JuergenMH/diver_led_tools/DiverFlasher/simulation/LEDS_in_Reihe/Boost_Converter.asc

C1: polcap; 100µ; V=25 Irms=750m Rser=0.16 Lser=0
C2: polcap; 47µ; V=25 Irms=750m Rser=0.16 Lser=0
C3: polcap; 100µ; V=25 Irms=750m Rser=0.16 Lser=0
C4: cap; 100n
D1: LED; LXK2-PW14
D2: LED; LXK2-PW14
D3: schottky; RB058LAM100
L1: ind; 33µ; Ipk=2.8 Rser=0.2 Rpar=86577.4 Cpar=0
L2: ind; 33µ; Ipk=2.8 Rser=0.2 Rpar=86577.4 Cpar=0
M1: nmos; NTB52N10
R1: res; 1
R2: res; 1K
V1: voltage; 3.6; Rser=0.1
V2: voltage; PULSE(0 5 0 0.1µ 0.1µ 27µ 40µ 500)
Named nets: 0, SW_IN, SW_OUT, U_BAT, U_OUT
.tran 0 1.6ms 0 0.1µs startup
IL1 / D3
Anlauf = 7,2mA (<1ms)
Min    = 0,8A
Max    = 3,3A
Mittel = 2A
25KHz
Zum Regler-Eingang
(AD-PIC)
Pulsweite gesteuert duch PIC-Controller
