JuergenMH/diver_led_tools/DiverFlasher/simulation/LEDS_Parallel/Boost_Converter.asc

C1: polcap; 100µ; V=25 Irms=750m Rser=0.16 Lser=0
C2: polcap; 47µ; V=25 Irms=750m Rser=0.16 Lser=0
C3: polcap; 470µ; V=25 Irms=750m Rser=0.16 Lser=0
D1: LED; LXK2-PW14
D2: LED; LXK2-PW14
D3: schottky; RB058LAM100
L1: ind; 330µ; Ipk=2.8 Rser=0.23 Rpar=86577.4 Cpar=0
L3: ind; 100µ; Ipk=4 Rser=0.2 Rpar=10000 Cpar=0
M1: nmos; NTB52N10
R1: res; 1; tol=2 pwr=1
R2: res; 1; tol=2 pwr=1
V1: voltage; 3.7; Rser=0.1
V2: voltage; PULSE(0 5 0 1µ 1µ 25µ 50µ 100)
Named nets: 0, SW_IN, SW_OUT, U_BAT, U_OUT
.tran 0 5ms 0 0.002ms startup
IL1
Max = 5,9A
Mittel = 2,7A
ID3
Max = 5,0A
Mittel = 3,0A
20KHz
